Tinkerforge/performance-stepper-bricklet/software/src/communication.h

/* performance-stepper-bricklet
 * Copyright (C) 2020 Olaf Lüke <olaf@tinkerforge.com>
 *
 * communication.h: TFP protocol message handling
 *
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
 * You should have received a copy of the GNU Lesser General Public
 * License along with this library; if not, write to the
 * Free Software Foundation, Inc., 59 Temple Place - Suite 330,
 * Boston, MA 02111-1307, USA.
 */

#ifndef COMMUNICATION_H
#define COMMUNICATION_H

#include <stdint.h>
#include <stdbool.h>

#include "bricklib2/protocols/tfp/tfp.h"
#include "bricklib2/bootloader/bootloader.h"

// Default functions
BootloaderHandleMessageResponse handle_message(const void *data, void *response);
void communication_tick(void);
void communication_init(void);

// Constants

#define PERFORMANCE_STEPPER_STEP_RESOLUTION_1 8
#define PERFORMANCE_STEPPER_STEP_RESOLUTION_2 7
#define PERFORMANCE_STEPPER_STEP_RESOLUTION_4 6
#define PERFORMANCE_STEPPER_STEP_RESOLUTION_8 5
#define PERFORMANCE_STEPPER_STEP_RESOLUTION_16 4
#define PERFORMANCE_STEPPER_STEP_RESOLUTION_32 3
#define PERFORMANCE_STEPPER_STEP_RESOLUTION_64 2
#define PERFORMANCE_STEPPER_STEP_RESOLUTION_128 1
#define PERFORMANCE_STEPPER_STEP_RESOLUTION_256 0

#define PERFORMANCE_STEPPER_RAMPING_MODE_POSITIONING 0
#define PERFORMANCE_STEPPER_RAMPING_MODE_VELOCITY_NEGATIVE 1
#define PERFORMANCE_STEPPER_RAMPING_MODE_VELOCITY_POSITIVE 2
#define PERFORMANCE_STEPPER_RAMPING_MODE_HOLD 3

#define PERFORMANCE_STEPPER_CHOPPER_MODE_SPREAD_CYCLE 0
#define PERFORMANCE_STEPPER_CHOPPER_MODE_FAST_DECAY 1

#define PERFORMANCE_STEPPER_FREEWHEEL_MODE_NORMAL 0
#define PERFORMANCE_STEPPER_FREEWHEEL_MODE_FREEWHEELING 1
#define PERFORMANCE_STEPPER_FREEWHEEL_MODE_COIL_SHORT_LS 2
#define PERFORMANCE_STEPPER_FREEWHEEL_MODE_COIL_SHORT_HS 3

#define PERFORMANCE_STEPPER_CURRENT_UP_STEP_INCREMENT_1 0
#define PERFORMANCE_STEPPER_CURRENT_UP_STEP_INCREMENT_2 1
#define PERFORMANCE_STEPPER_CURRENT_UP_STEP_INCREMENT_4 2
#define PERFORMANCE_STEPPER_CURRENT_UP_STEP_INCREMENT_8 3

#define PERFORMANCE_STEPPER_CURRENT_DOWN_STEP_DECREMENT_1 0
#define PERFORMANCE_STEPPER_CURRENT_DOWN_STEP_DECREMENT_2 1
#define PERFORMANCE_STEPPER_CURRENT_DOWN_STEP_DECREMENT_8 2
#define PERFORMANCE_STEPPER_CURRENT_DOWN_STEP_DECREMENT_32 3

#define PERFORMANCE_STEPPER_MINIMUM_CURRENT_HALF 0
#define PERFORMANCE_STEPPER_MINIMUM_CURRENT_QUARTER 1

#define PERFORMANCE_STEPPER_STALLGUARD_MODE_STANDARD 0
#define PERFORMANCE_STEPPER_STALLGUARD_MODE_FILTERED 1

#define PERFORMANCE_STEPPER_OPEN_LOAD_NONE 0
#define PERFORMANCE_STEPPER_OPEN_LOAD_PHASE_A 1
#define PERFORMANCE_STEPPER_OPEN_LOAD_PHASE_B 2
#define PERFORMANCE_STEPPER_OPEN_LOAD_PHASE_AB 3

#define PERFORMANCE_STEPPER_SHORT_TO_GROUND_NONE 0
#define PERFORMANCE_STEPPER_SHORT_TO_GROUND_PHASE_A 1
#define PERFORMANCE_STEPPER_SHORT_TO_GROUND_PHASE_B 2
#define PERFORMANCE_STEPPER_SHORT_TO_GROUND_PHASE_AB 3

#define PERFORMANCE_STEPPER_OVER_TEMPERATURE_NONE 0
#define PERFORMANCE_STEPPER_OVER_TEMPERATURE_WARNING 1
#define PERFORMANCE_STEPPER_OVER_TEMPERATURE_LIMIT 2

#define PERFORMANCE_STEPPER_STATE_STOP 1
#define PERFORMANCE_STEPPER_STATE_ACCELERATION 2
#define PERFORMANCE_STEPPER_STATE_RUN 3
#define PERFORMANCE_STEPPER_STATE_DEACCELERATION 4
#define PERFORMANCE_STEPPER_STATE_DIRECTION_CHANGE_TO_FORWARD 5
#define PERFORMANCE_STEPPER_STATE_DIRECTION_CHANGE_TO_BACKWARD 6

#define PERFORMANCE_STEPPER_GPIO_ACTION_NONE 0
#define PERFORMANCE_STEPPER_GPIO_ACTION_NORMAL_STOP_RISING_EDGE 1
#define PERFORMANCE_STEPPER_GPIO_ACTION_NORMAL_STOP_FALLING_EDGE 2
#define PERFORMANCE_STEPPER_GPIO_ACTION_EMERGENCY_STOP_RISING_EDGE 4
#define PERFORMANCE_STEPPER_GPIO_ACTION_EMERGENCY_STOP_FALLING_EDGE 8
#define PERFORMANCE_STEPPER_GPIO_ACTION_CALLBACK_RISING_EDGE 16
#define PERFORMANCE_STEPPER_GPIO_ACTION_CALLBACK_FALLING_EDGE 32

#define PERFORMANCE_STEPPER_ERROR_LED_CONFIG_OFF 0
#define PERFORMANCE_STEPPER_ERROR_LED_CONFIG_ON 1
#define PERFORMANCE_STEPPER_ERROR_LED_CONFIG_SHOW_HEARTBEAT 2
#define PERFORMANCE_STEPPER_ERROR_LED_CONFIG_SHOW_ERROR 3

#define PERFORMANCE_STEPPER_ENABLE_LED_CONFIG_OFF 0
#define PERFORMANCE_STEPPER_ENABLE_LED_CONFIG_ON 1
#define PERFORMANCE_STEPPER_ENABLE_LED_CONFIG_SHOW_HEARTBEAT 2
#define PERFORMANCE_STEPPER_ENABLE_LED_CONFIG_SHOW_ENABLE 3

#define PERFORMANCE_STEPPER_STEPS_LED_CONFIG_OFF 0
#define PERFORMANCE_STEPPER_STEPS_LED_CONFIG_ON 1
#define PERFORMANCE_STEPPER_STEPS_LED_CONFIG_SHOW_HEARTBEAT 2
#define PERFORMANCE_STEPPER_STEPS_LED_CONFIG_SHOW_STEPS 3

#define PERFORMANCE_STEPPER_GPIO_LED_CONFIG_OFF 0
#define PERFORMANCE_STEPPER_GPIO_LED_CONFIG_ON 1
#define PERFORMANCE_STEPPER_GPIO_LED_CONFIG_SHOW_HEARTBEAT 2
#define PERFORMANCE_STEPPER_GPIO_LED_CONFIG_SHOW_GPIO_ACTIVE_HIGH 3
#define PERFORMANCE_STEPPER_GPIO_LED_CONFIG_SHOW_GPIO_ACTIVE_LOW 4

#define PERFORMANCE_STEPPER_FILTER_TIME_100 0
#define PERFORMANCE_STEPPER_FILTER_TIME_200 1
#define PERFORMANCE_STEPPER_FILTER_TIME_300 2
#define PERFORMANCE_STEPPER_FILTER_TIME_400 3

#define PERFORMANCE_STEPPER_SPIKE_FILTER_BANDWIDTH_100 0
#define PERFORMANCE_STEPPER_SPIKE_FILTER_BANDWIDTH_1000 1
#define PERFORMANCE_STEPPER_SPIKE_FILTER_BANDWIDTH_2000 2
#define PERFORMANCE_STEPPER_SPIKE_FILTER_BANDWIDTH_3000 3

#define PERFORMANCE_STEPPER_BOOTLOADER_MODE_BOOTLOADER 0
#define PERFORMANCE_STEPPER_BOOTLOADER_MODE_FIRMWARE 1
#define PERFORMANCE_STEPPER_BOOTLOADER_MODE_BOOTLOADER_WAIT_FOR_REBOOT 2
#define PERFORMANCE_STEPPER_BOOTLOADER_MODE_FIRMWARE_WAIT_FOR_REBOOT 3
#define PERFORMANCE_STEPPER_BOOTLOADER_MODE_FIRMWARE_WAIT_FOR_ERASE_AND_REBOOT 4

#define PERFORMANCE_STEPPER_BOOTLOADER_STATUS_OK 0
#define PERFORMANCE_STEPPER_BOOTLOADER_STATUS_INVALID_MODE 1
#define PERFORMANCE_STEPPER_BOOTLOADER_STATUS_NO_CHANGE 2
#define PERFORMANCE_STEPPER_BOOTLOADER_STATUS_ENTRY_FUNCTION_NOT_PRESENT 3
#define PERFORMANCE_STEPPER_BOOTLOADER_STATUS_DEVICE_IDENTIFIER_INCORRECT 4
#define PERFORMANCE_STEPPER_BOOTLOADER_STATUS_CRC_MISMATCH 5

#define PERFORMANCE_STEPPER_STATUS_LED_CONFIG_OFF 0
#define PERFORMANCE_STEPPER_STATUS_LED_CONFIG_ON 1
#define PERFORMANCE_STEPPER_STATUS_LED_CONFIG_SHOW_HEARTBEAT 2
#define PERFORMANCE_STEPPER_STATUS_LED_CONFIG_SHOW_STATUS 3

// Function and callback IDs and structs
#define FID_SET_MOTION_CONFIGURATION 1
#define FID_GET_MOTION_CONFIGURATION 2
#define FID_SET_CURRENT_POSITION 3
#define FID_GET_CURRENT_POSITION 4
#define FID_GET_CURRENT_VELOCITY 5
#define FID_SET_TARGET_POSITION 6
#define FID_GET_TARGET_POSITION 7
#define FID_SET_STEPS 8
#define FID_GET_STEPS 9
#define FID_GET_REMAINING_STEPS 10
#define FID_SET_STEP_CONFIGURATION 11
#define FID_GET_STEP_CONFIGURATION 12
#define FID_SET_MOTOR_CURRENT 22
#define FID_GET_MOTOR_CURRENT 23
#define FID_SET_ENABLED 24
#define FID_GET_ENABLED 25
#define FID_SET_BASIC_CONFIGURATION 26
#define FID_GET_BASIC_CONFIGURATION 27
#define FID_SET_SPREADCYCLE_CONFIGURATION 28
#define FID_GET_SPREADCYCLE_CONFIGURATION 29
#define FID_SET_STEALTH_CONFIGURATION 30
#define FID_GET_STEALTH_CONFIGURATION 31
#define FID_SET_COOLSTEP_CONFIGURATION 32
#define FID_GET_COOLSTEP_CONFIGURATION 33
#define FID_SET_SHORT_CONFIGURATION 34
#define FID_GET_SHORT_CONFIGURATION 35
#define FID_GET_DRIVER_STATUS 36
#define FID_GET_INPUT_VOLTAGE 37
#define FID_GET_TEMPERATURE 38
#define FID_SET_GPIO_CONFIGURATION 39
#define FID_GET_GPIO_CONFIGURATION 40
#define FID_SET_GPIO_ACTION 41
#define FID_GET_GPIO_ACTION 42
#define FID_GET_GPIO_STATE 43
#define FID_SET_ERROR_LED_CONFIG 44
#define FID_GET_ERROR_LED_CONFIG 45
#define FID_SET_ENABLE_LED_CONFIG 46
#define FID_GET_ENABLE_LED_CONFIG 47
#define FID_SET_STEPS_LED_CONFIG 48
#define FID_GET_STEPS_LED_CONFIG 49
#define FID_SET_GPIO_LED_CONFIG 50
#define FID_GET_GPIO_LED_CONFIG 51
#define FID_WRITE_REGISTER 52
#define FID_READ_REGISTER 53


typedef struct {
	TFPMessageHeader header;
	uint8_t ramping_mode;
	int32_t velocity_start;
	int32_t acceleration_1;
	int32_t velocity_1;
	int32_t acceleration_max;
	int32_t velocity_max;
	int32_t deceleration_max;
	int32_t deceleration_1;
	int32_t velocity_stop;
	int32_t ramp_zero_wait;
} __attribute__((__packed__)) SetMotionConfiguration;

typedef struct {
	TFPMessageHeader header;
} __attribute__((__packed__)) GetMotionConfiguration;

typedef struct {
	TFPMessageHeader header;
	uint8_t ramping_mode;
	int32_t velocity_start;
	int32_t acceleration_1;
	int32_t velocity_1;
	int32_t acceleration_max;
	int32_t velocity_max;
	int32_t deceleration_max;
	int32_t deceleration_1;
	int32_t velocity_stop;
	int32_t ramp_zero_wait;
} __attribute__((__packed__)) GetMotionConfiguration_Response;

typedef struct {
	TFPMessageHeader header;
	int32_t position;
} __attribute__((__packed__)) SetCurrentPosition;

typedef struct {
	TFPMessageHeader header;
} __attribute__((__packed__)) GetCurrentPosition;

typedef struct {
	TFPMessageHeader header;
	int32_t position;
} __attribute__((__packed__)) GetCurrentPosition_Response;

typedef struct {
	TFPMessageHeader header;
} __attribute__((__packed__)) GetCurrentVelocity;

typedef struct {
	TFPMessageHeader header;
	int32_t velocity;
} __attribute__((__packed__)) GetCurrentVelocity_Response;

typedef struct {
	TFPMessageHeader header;
	int32_t position;
} __attribute__((__packed__)) SetTargetPosition;

typedef struct {
	TFPMessageHeader header;
} __attribute__((__packed__)) GetTargetPosition;

typedef struct {
	TFPMessageHeader header;
	int32_t position;
} __attribute__((__packed__)) GetTargetPosition_Response;

typedef struct {
	TFPMessageHeader header;
	int32_t steps;
} __attribute__((__packed__)) SetSteps;

typedef struct {
	TFPMessageHeader header;
} __attribute__((__packed__)) GetSteps;

typedef struct {
	TFPMessageHeader header;
	int32_t steps;
} __attribute__((__packed__)) GetSteps_Response;

typedef struct {
	TFPMessageHeader header;
} __attribute__((__packed__)) GetRemainingSteps;

typedef struct {
	TFPMessageHeader header;
	int32_t steps;
} __attribute__((__packed__)) GetRemainingSteps_Response;

typedef struct {
	TFPMessageHeader header;
	uint8_t step_resolution;
	bool interpolation;
} __attribute__((__packed__)) SetStepConfiguration;

typedef struct {
	TFPMessageHeader header;
} __attribute__((__packed__)) GetStepConfiguration;

typedef struct {
	TFPMessageHeader header;
	uint8_t step_resolution;
	bool interpolation;
} __attribute__((__packed__)) GetStepConfiguration_Response;

typedef struct {
	TFPMessageHeader header;
	uint16_t current;
} __attribute__((__packed__)) SetMotorCurrent;

typedef struct {
	TFPMessageHeader header;
} __attribute__((__packed__)) GetMotorCurrent;

typedef struct {
	TFPMessageHeader header;
	uint16_t current;
} __attribute__((__packed__)) GetMotorCurrent_Response;

typedef struct {
	TFPMessageHeader header;
	bool enabled;
} __attribute__((__packed__)) SetEnabled;

typedef struct {
	TFPMessageHeader header;
} __attribute__((__packed__)) GetEnabled;

typedef struct {
	TFPMessageHeader header;
	bool enabled;
} __attribute__((__packed__)) GetEnabled_Response;

typedef struct {
	TFPMessageHeader header;
	uint16_t standstill_current;
	uint16_t motor_run_current;
	uint16_t standstill_delay_time;
	uint16_t power_down_time;
	uint16_t stealth_threshold;
	uint16_t coolstep_threshold;
	uint16_t classic_threshold;
	bool high_velocity_chopper_mode;
} __attribute__((__packed__)) SetBasicConfiguration;

typedef struct {
	TFPMessageHeader header;
} __attribute__((__packed__)) GetBasicConfiguration;

typedef struct {
	TFPMessageHeader header;
	uint16_t standstill_current;
	uint16_t motor_run_current;
	uint16_t standstill_delay_time;
	uint16_t power_down_time;
	uint16_t stealth_threshold;
	uint16_t coolstep_threshold;
	uint16_t classic_threshold;
	bool high_velocity_chopper_mode;
} __attribute__((__packed__)) GetBasicConfiguration_Response;

typedef struct {
	TFPMessageHeader header;
	uint8_t slow_decay_duration;
	bool high_velocity_fullstep;
	uint8_t fast_decay_duration;
	uint8_t hysteresis_start_value;
	int8_t hysteresis_end_value;
	int8_t sine_wave_offset;
	uint8_t chopper_mode;
	uint8_t comparator_blank_time;
	bool fast_decay_without_comparator;
} __attribute__((__packed__)) SetSpreadcycleConfiguration;

typedef struct {
	TFPMessageHeader header;
} __attribute__((__packed__)) GetSpreadcycleConfiguration;

typedef struct {
	TFPMessageHeader header;
	uint8_t slow_decay_duration;
	bool high_velocity_fullstep;
	bool enable_random_slow_decay;
	uint8_t fast_decay_duration;
	uint8_t hysteresis_start_value;
	int8_t hysteresis_end_value;
	int8_t sine_wave_offset;
	uint8_t chopper_mode;
	uint8_t comparator_blank_time;
	bool fast_decay_without_comparator;
} __attribute__((__packed__)) GetSpreadcycleConfiguration_Response;

typedef struct {
	TFPMessageHeader header;
	bool enable_stealth;
	uint8_t offset;
	uint8_t gradient;
	bool enable_autoscale;
	bool enable_autogradient;
	uint8_t freewheel_mode;
	uint8_t regulation_loop_gradient;
	uint8_t amplitude_limit;
} __attribute__((__packed__)) SetStealthConfiguration;

typedef struct {
	TFPMessageHeader header;
} __attribute__((__packed__)) GetStealthConfiguration;

typedef struct {
	TFPMessageHeader header;
	bool enable_stealth;
	uint8_t offset;
	uint8_t gradient;
	bool enable_autoscale;
	bool enable_autogradient;
	uint8_t freewheel_mode;
	uint8_t regulation_loop_gradient;
	uint8_t amplitude_limit;
} __attribute__((__packed__)) GetStealthConfiguration_Response;

typedef struct {
	TFPMessageHeader header;
	uint8_t minimum_stallguard_value;
	uint8_t maximum_stallguard_value;
	uint8_t current_up_step_width;
	uint8_t current_down_step_width;
	uint8_t minimum_current;
	int8_t stallguard_threshold_value;
	uint8_t stallguard_mode;
} __attribute__((__packed__)) SetCoolstepConfiguration;

typedef struct {
	TFPMessageHeader header;
} __attribute__((__packed__)) GetCoolstepConfiguration;

typedef struct {
	TFPMessageHeader header;
	uint8_t minimum_stallguard_value;
	uint8_t maximum_stallguard_value;
	uint8_t current_up_step_width;
	uint8_t current_down_step_width;
	uint8_t minimum_current;
	int8_t stallguard_threshold_value;
	uint8_t stallguard_mode;
} __attribute__((__packed__)) GetCoolstepConfiguration_Response;

typedef struct {
	TFPMessageHeader header;
	bool disable_short_to_voltage_protection;
	bool disable_short_to_ground_protection;
	uint8_t short_to_voltage_level;
	uint8_t short_to_ground_level;
	uint8_t spike_filter_bandwidth;
	bool short_detection_delay;
	uint8_t filter_time;
} __attribute__((__packed__)) SetShortConfiguration;

typedef struct {
	TFPMessageHeader header;
} __attribute__((__packed__)) GetShortConfiguration;

typedef struct {
	TFPMessageHeader header;
	bool disable_short_to_voltage_protection;
	bool disable_short_to_ground_protection;
	uint8_t short_to_voltage_level;
	uint8_t short_to_ground_level;
	uint8_t spike_filter_bandwidth;
	bool short_detection_delay;
	uint8_t filter_time;
} __attribute__((__packed__)) GetShortConfiguration_Response;

typedef struct {
	TFPMessageHeader header;
} __attribute__((__packed__)) GetDriverStatus;

typedef struct {
	TFPMessageHeader header;
	uint8_t open_load;
	uint8_t short_to_ground;
	uint8_t over_temperature;
	bool motor_stalled;
	uint8_t actual_motor_current;
	bool full_step_active;
	uint8_t stallguard_result;
	uint8_t stealth_voltage_amplitude;
} __attribute__((__packed__)) GetDriverStatus_Response;

typedef struct {
	TFPMessageHeader header;
} __attribute__((__packed__)) GetInputVoltage;

typedef struct {
	TFPMessageHeader header;
	uint16_t voltage;
} __attribute__((__packed__)) GetInputVoltage_Response;

typedef struct {
	TFPMessageHeader header;
} __attribute__((__packed__)) GetTemperature;

typedef struct {
	TFPMessageHeader header;
	int16_t temperature;
} __attribute__((__packed__)) GetTemperature_Response;

typedef struct {
	TFPMessageHeader header;
	uint16_t debounce;
	int32_t stop_deceleration;
} __attribute__((__packed__)) SetGPIOConfiguration;

typedef struct {
	TFPMessageHeader header;
} __attribute__((__packed__)) GetGPIOConfiguration;

typedef struct {
	TFPMessageHeader header;
	uint16_t debounce;
	int32_t stop_deceleration;
} __attribute__((__packed__)) GetGPIOConfiguration_Response;

typedef struct {
	TFPMessageHeader header;
	uint8_t channel;
	uint32_t action;
} __attribute__((__packed__)) SetGPIOAction;

typedef struct {
	TFPMessageHeader header;
	uint8_t channel;
} __attribute__((__packed__)) GetGPIOAction;

typedef struct {
	TFPMessageHeader header;
	uint32_t action;
} __attribute__((__packed__)) GetGPIOAction_Response;

typedef struct {
	TFPMessageHeader header;
} __attribute__((__packed__)) GetGPIOState;

typedef struct {
	TFPMessageHeader header;
	uint8_t gpio_state[1];
} __attribute__((__packed__)) GetGPIOState_Response;

typedef struct {
	TFPMessageHeader header;
	uint8_t config;
} __attribute__((__packed__)) SetErrorLEDConfig;

typedef struct {
	TFPMessageHeader header;
} __attribute__((__packed__)) GetErrorLEDConfig;

typedef struct {
	TFPMessageHeader header;
	uint8_t config;
} __attribute__((__packed__)) GetErrorLEDConfig_Response;

typedef struct {
	TFPMessageHeader header;
	uint8_t config;
} __attribute__((__packed__)) SetEnableLEDConfig;

typedef struct {
	TFPMessageHeader header;
} __attribute__((__packed__)) GetEnableLEDConfig;

typedef struct {
	TFPMessageHeader header;
	uint8_t config;
} __attribute__((__packed__)) GetEnableLEDConfig_Response;

typedef struct {
	TFPMessageHeader header;
	uint8_t config;
} __attribute__((__packed__)) SetStepsLEDConfig;

typedef struct {
	TFPMessageHeader header;
} __attribute__((__packed__)) GetStepsLEDConfig;

typedef struct {
	TFPMessageHeader header;
	uint8_t config;
} __attribute__((__packed__)) GetStepsLEDConfig_Response;

typedef struct {
	TFPMessageHeader header;
	uint8_t channel;
	uint8_t config;
} __attribute__((__packed__)) SetGPIOLEDConfig;

typedef struct {
	TFPMessageHeader header;
	uint8_t channel;
} __attribute__((__packed__)) GetGPIOLEDConfig;

typedef struct {
	TFPMessageHeader header;
	uint8_t config;
} __attribute__((__packed__)) GetGPIOLEDConfig_Response;

typedef struct {
	TFPMessageHeader header;
	uint8_t reg;
	uint32_t value;
} __attribute__((__packed__)) WriteRegister;

typedef struct {
	TFPMessageHeader header;
	uint8_t status;
} __attribute__((__packed__)) WriteRegister_Response;

typedef struct {
	TFPMessageHeader header;
	uint8_t reg;
} __attribute__((__packed__)) ReadRegister;

typedef struct {
	TFPMessageHeader header;
	uint8_t status;
	uint32_t value;
} __attribute__((__packed__)) ReadRegister_Response;


// Function prototypes
BootloaderHandleMessageResponse set_motion_configuration(const SetMotionConfiguration *data);
BootloaderHandleMessageResponse get_motion_configuration(const GetMotionConfiguration *data, GetMotionConfiguration_Response *response);
BootloaderHandleMessageResponse set_current_position(const SetCurrentPosition *data);
BootloaderHandleMessageResponse get_current_position(const GetCurrentPosition *data, GetCurrentPosition_Response *response);
BootloaderHandleMessageResponse get_current_velocity(const GetCurrentVelocity *data, GetCurrentVelocity_Response *response);
BootloaderHandleMessageResponse set_target_position(const SetTargetPosition *data);
BootloaderHandleMessageResponse get_target_position(const GetTargetPosition *data, GetTargetPosition_Response *response);
BootloaderHandleMessageResponse set_steps(const SetSteps *data);
BootloaderHandleMessageResponse get_steps(const GetSteps *data, GetSteps_Response *response);
BootloaderHandleMessageResponse get_remaining_steps(const GetRemainingSteps *data, GetRemainingSteps_Response *response);
BootloaderHandleMessageResponse set_step_configuration(const SetStepConfiguration *data);
BootloaderHandleMessageResponse get_step_configuration(const GetStepConfiguration *data, GetStepConfiguration_Response *response);
BootloaderHandleMessageResponse set_motor_current(const SetMotorCurrent *data);
BootloaderHandleMessageResponse get_motor_current(const GetMotorCurrent *data, GetMotorCurrent_Response *response);
BootloaderHandleMessageResponse set_enabled(const SetEnabled *data);
BootloaderHandleMessageResponse get_enabled(const GetEnabled *data, GetEnabled_Response *response);
BootloaderHandleMessageResponse set_basic_configuration(const SetBasicConfiguration *data);
BootloaderHandleMessageResponse get_basic_configuration(const GetBasicConfiguration *data, GetBasicConfiguration_Response *response);
BootloaderHandleMessageResponse set_spreadcycle_configuration(const SetSpreadcycleConfiguration *data);
BootloaderHandleMessageResponse get_spreadcycle_configuration(const GetSpreadcycleConfiguration *data, GetSpreadcycleConfiguration_Response *response);
BootloaderHandleMessageResponse set_stealth_configuration(const SetStealthConfiguration *data);
BootloaderHandleMessageResponse get_stealth_configuration(const GetStealthConfiguration *data, GetStealthConfiguration_Response *response);
BootloaderHandleMessageResponse set_coolstep_configuration(const SetCoolstepConfiguration *data);
BootloaderHandleMessageResponse get_coolstep_configuration(const GetCoolstepConfiguration *data, GetCoolstepConfiguration_Response *response);
BootloaderHandleMessageResponse set_short_configuration(const SetShortConfiguration *data);
BootloaderHandleMessageResponse get_short_configuration(const GetShortConfiguration *data, GetShortConfiguration_Response *response);
BootloaderHandleMessageResponse get_driver_status(const GetDriverStatus *data, GetDriverStatus_Response *response);
BootloaderHandleMessageResponse get_input_voltage(const GetInputVoltage *data, GetInputVoltage_Response *response);
BootloaderHandleMessageResponse get_temperature(const GetTemperature *data, GetTemperature_Response *response);
BootloaderHandleMessageResponse set_gpio_configuration(const SetGPIOConfiguration *data);
BootloaderHandleMessageResponse get_gpio_configuration(const GetGPIOConfiguration *data, GetGPIOConfiguration_Response *response);
BootloaderHandleMessageResponse set_gpio_action(const SetGPIOAction *data);
BootloaderHandleMessageResponse get_gpio_action(const GetGPIOAction *data, GetGPIOAction_Response *response);
BootloaderHandleMessageResponse get_gpio_state(const GetGPIOState *data, GetGPIOState_Response *response);
BootloaderHandleMessageResponse set_error_led_config(const SetErrorLEDConfig *data);
BootloaderHandleMessageResponse get_error_led_config(const GetErrorLEDConfig *data, GetErrorLEDConfig_Response *response);
BootloaderHandleMessageResponse set_enable_led_config(const SetEnableLEDConfig *data);
BootloaderHandleMessageResponse get_enable_led_config(const GetEnableLEDConfig *data, GetEnableLEDConfig_Response *response);
BootloaderHandleMessageResponse set_steps_led_config(const SetStepsLEDConfig *data);
BootloaderHandleMessageResponse get_steps_led_config(const GetStepsLEDConfig *data, GetStepsLEDConfig_Response *response);
BootloaderHandleMessageResponse set_gpio_led_config(const SetGPIOLEDConfig *data);
BootloaderHandleMessageResponse get_gpio_led_config(const GetGPIOLEDConfig *data, GetGPIOLEDConfig_Response *response);
BootloaderHandleMessageResponse write_register(const WriteRegister *data, WriteRegister_Response *response);
BootloaderHandleMessageResponse read_register(const ReadRegister *data, ReadRegister_Response *response);

// Callbacks


#define COMMUNICATION_CALLBACK_TICK_WAIT_MS 1
#define COMMUNICATION_CALLBACK_HANDLER_NUM 0
#define COMMUNICATION_CALLBACK_LIST_INIT \


#endif
